haldarsaurav/train_bus_weather_signboard/docs/images/screen_boot.png

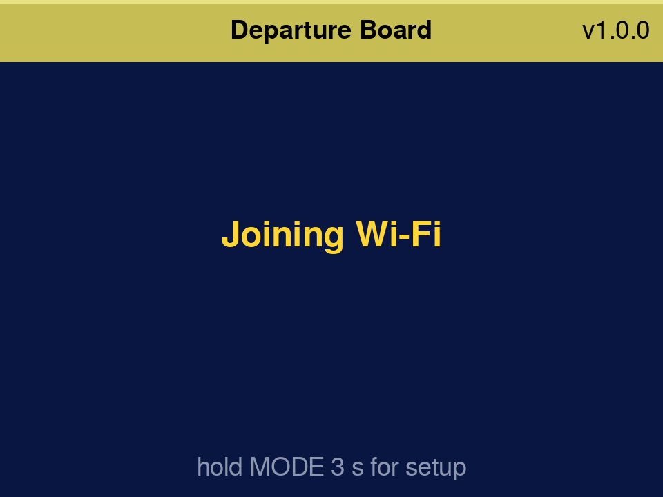
docs/images/screen_boot.png
