haldarsaurav/train_bus_weather_signboard/docs/images/screen_hold_hint.png

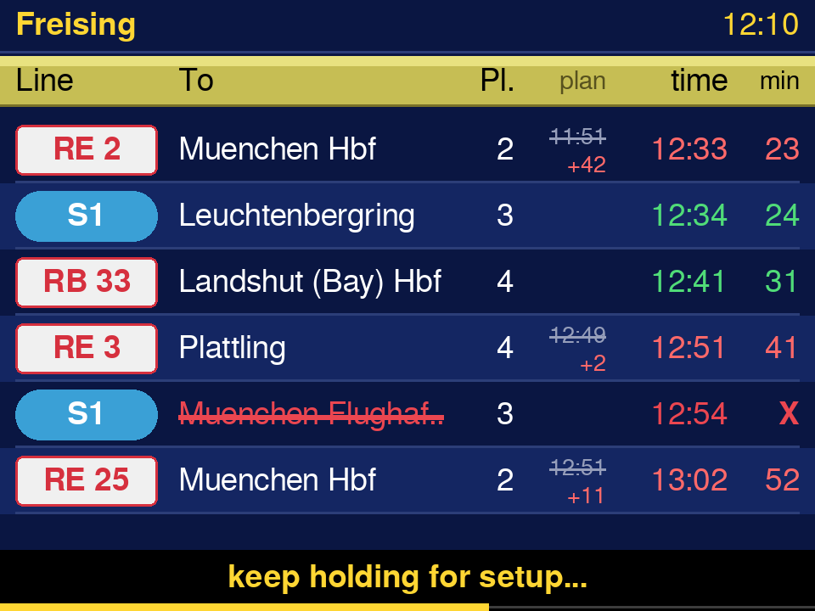
docs/images/screen_hold_hint.png
