haldarsaurav/train_bus_weather_signboard/docs/previews_v1.2.0/A_1_boot.png

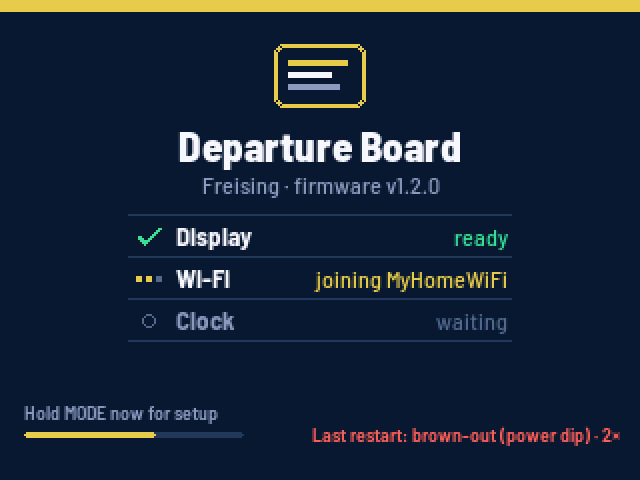
docs/previews_v1.2.0/A_1_boot.png
