haldarsaurav/train_bus_weather_signboard/docs/previews_v1.2.0/A_4_pr.png

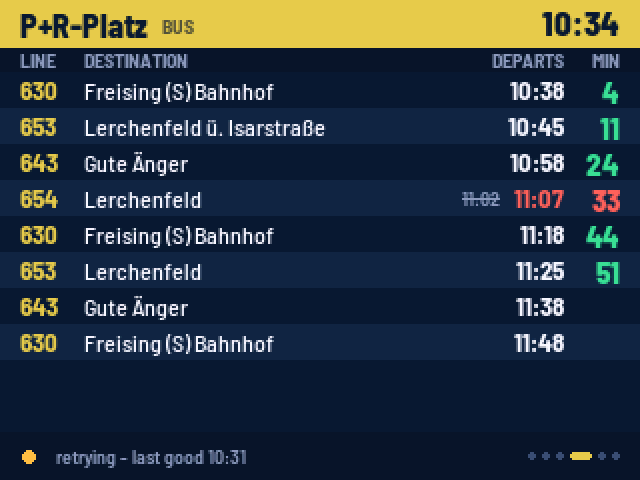
docs/previews_v1.2.0/A_4_pr.png
