haldarsaurav/train_bus_weather_signboard/docs/previews_v1.2.0/B_1_boot.png

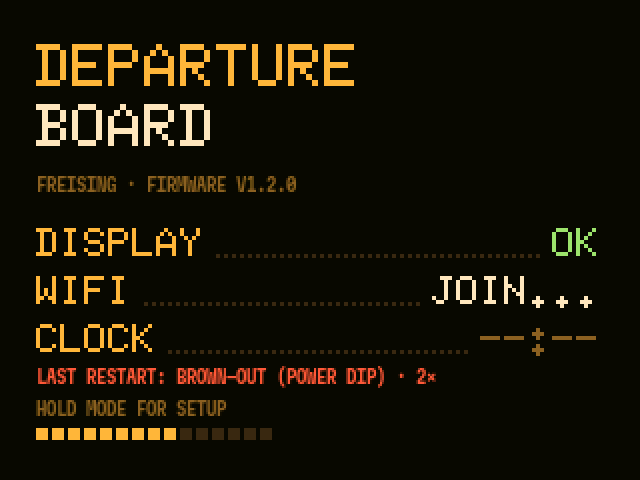
docs/previews_v1.2.0/B_1_boot.png
