haldarsaurav/train_bus_weather_signboard/docs/previews_v1.2.0/B_7_hold.png

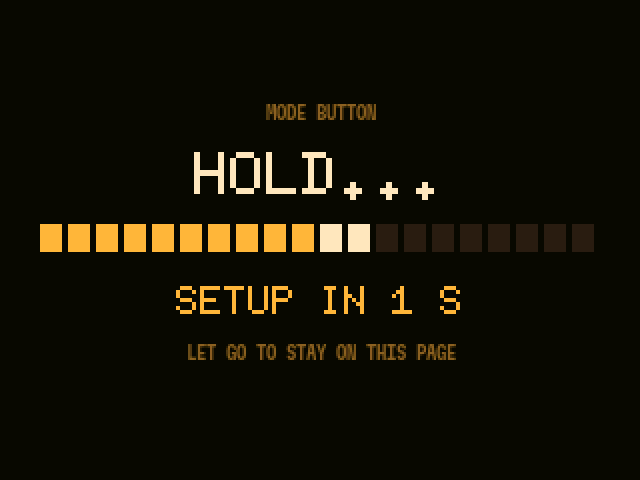
docs/previews_v1.2.0/B_7_hold.png
