haldarsaurav/train_bus_weather_signboard/docs/previews_v1.2.0/C_1_boot.png

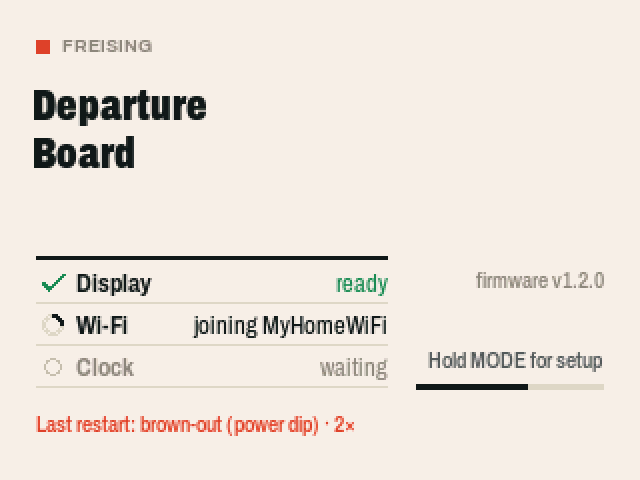
docs/previews_v1.2.0/C_1_boot.png
