haldarsaurav/train_bus_weather_signboard/docs/previews_v1.2.0/C_2b_trains_page2.png

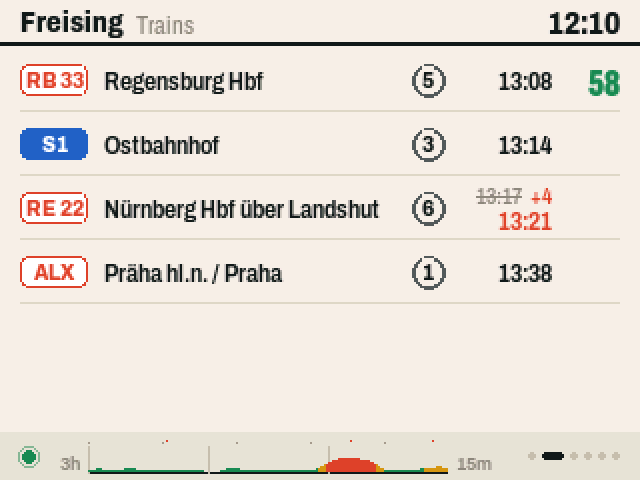
docs/previews_v1.2.0/C_2b_trains_page2.png
