haldarsaurav/train_bus_weather_signboard/docs/previews_v1.2.0/F_3_stadtbus.png

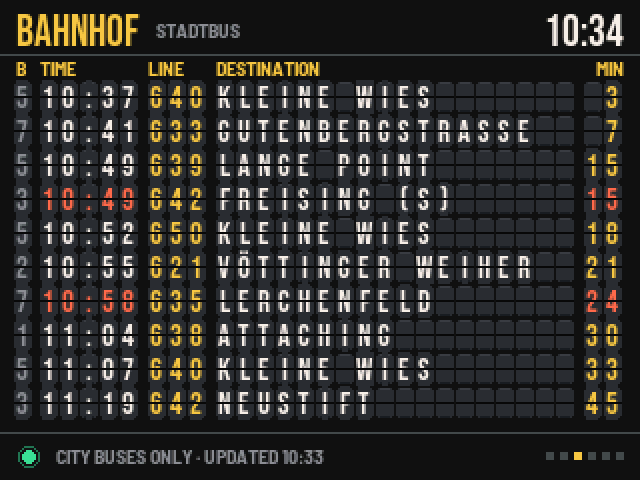
docs/previews_v1.2.0/F_3_stadtbus.png
