haldarsaurav/train_bus_weather_signboard/docs/previews_v1.2.0/F_4_pr.png

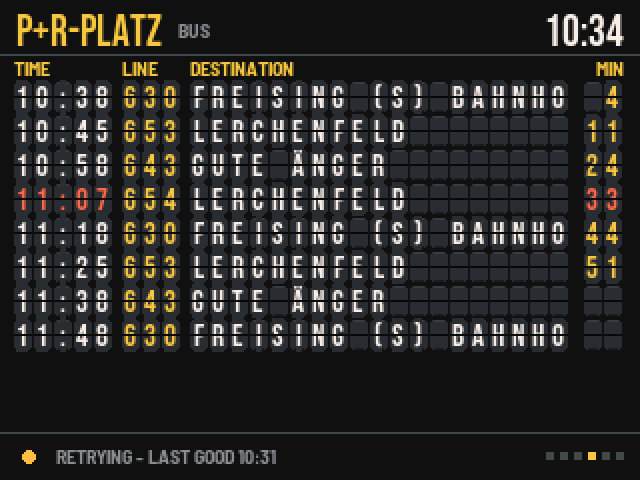
docs/previews_v1.2.0/F_4_pr.png
