haldarsaurav/train_bus_weather_signboard/docs/previews_v1.2.0/F_stress_umlauts_emoji.png

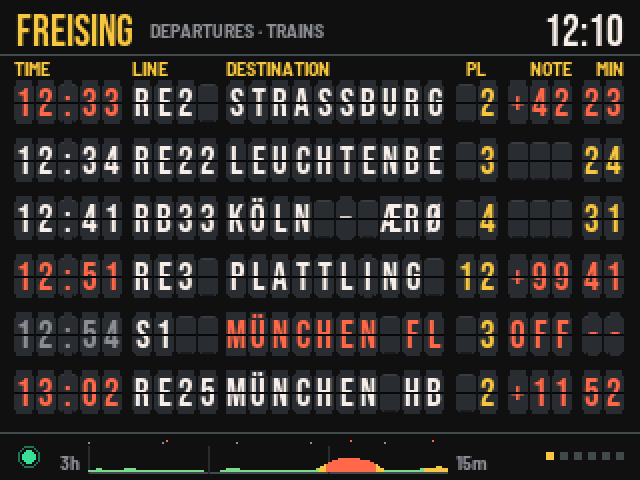
docs/previews_v1.2.0/F_stress_umlauts_emoji.png
