haldarsaurav/train_bus_weather_signboard/docs/previews_v1.2.0/O_5_weather.png

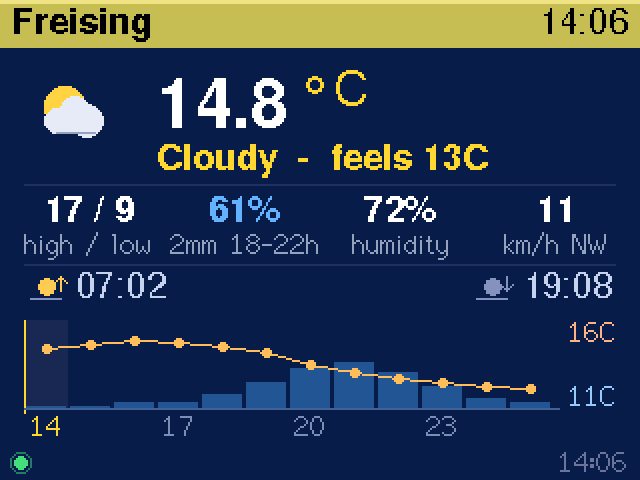
docs/previews_v1.2.0/O_5_weather.png
