haldarsaurav/train_bus_weather_signboard/docs/previews_v1.2.0/O_9_empty_trains.png

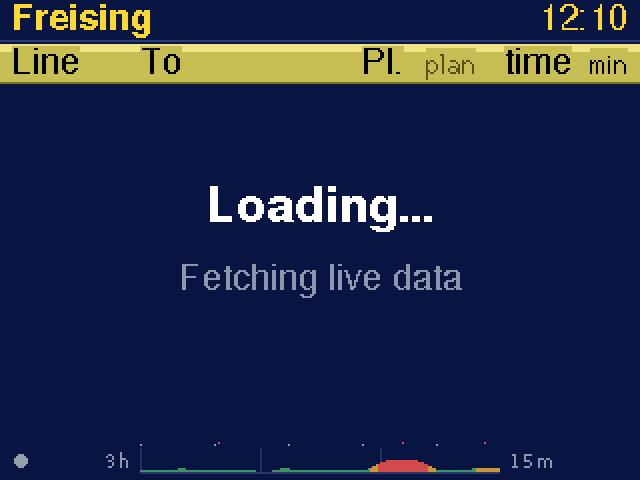
docs/previews_v1.2.0/O_9_empty_trains.png
