haldarsaurav/train_bus_weather_signboard/docs/previews_v1.2.0/portal_1.png

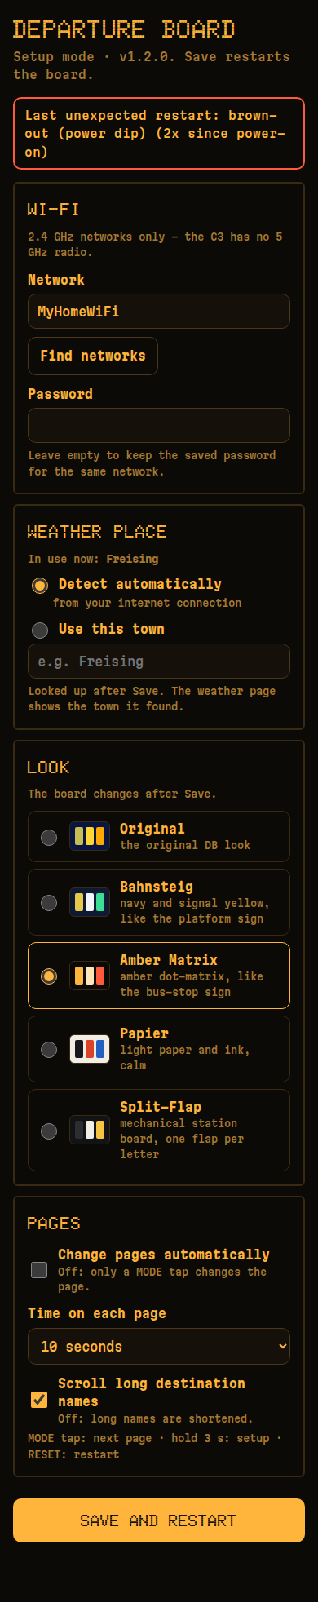
docs/previews_v1.2.0/portal_1.png
