haldarsaurav/train_bus_weather_signboard/docs/images/screen_setup.png

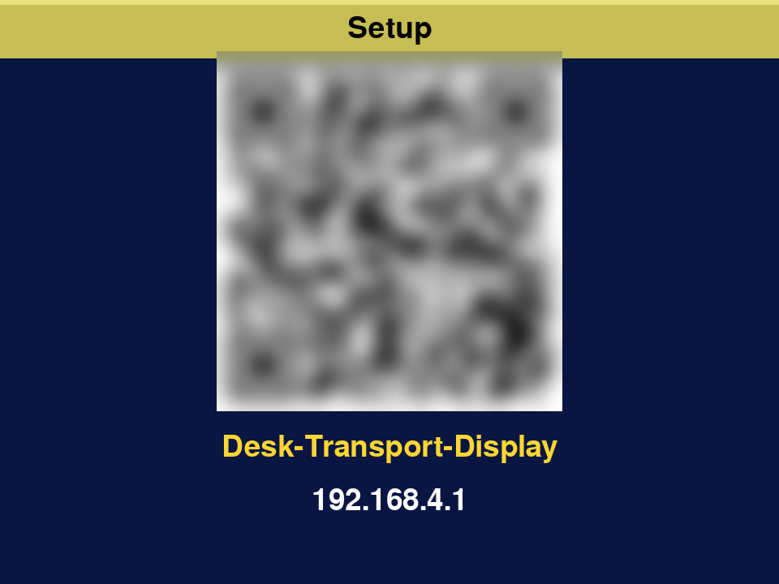
docs/images/screen_setup.png
