haldarsaurav/train_bus_weather_signboard/docs/images/wiring.png

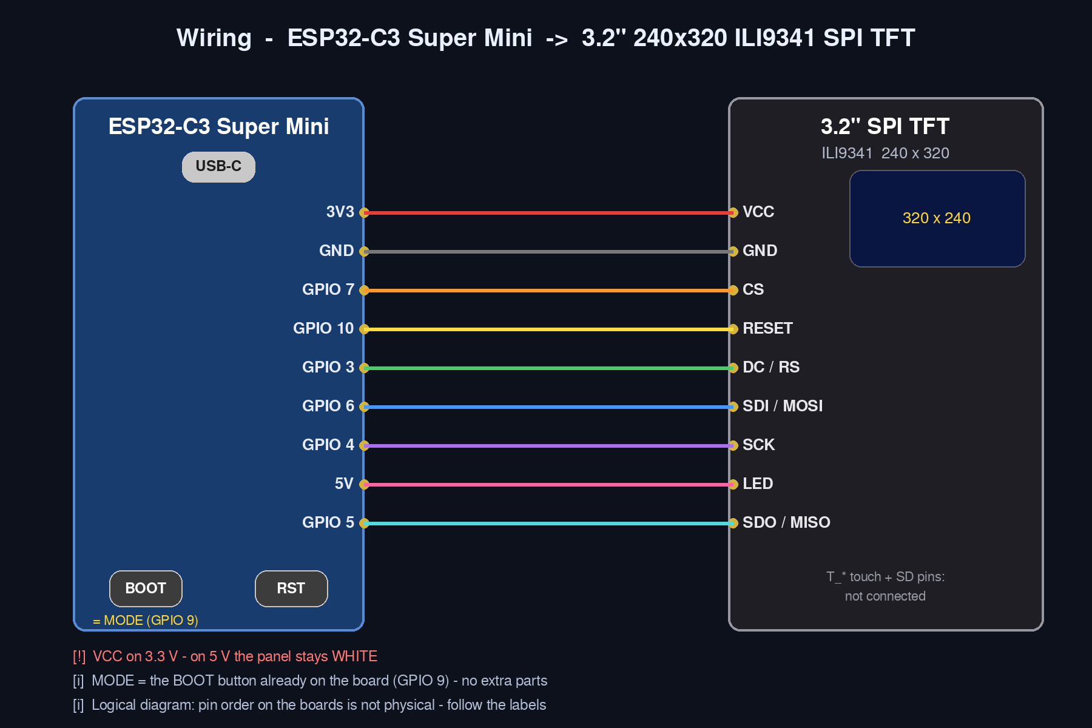
docs/images/wiring.png
