haldarsaurav/train_bus_weather_signboard/docs/previews_v1.2.0/A_8b_setup_phone.png

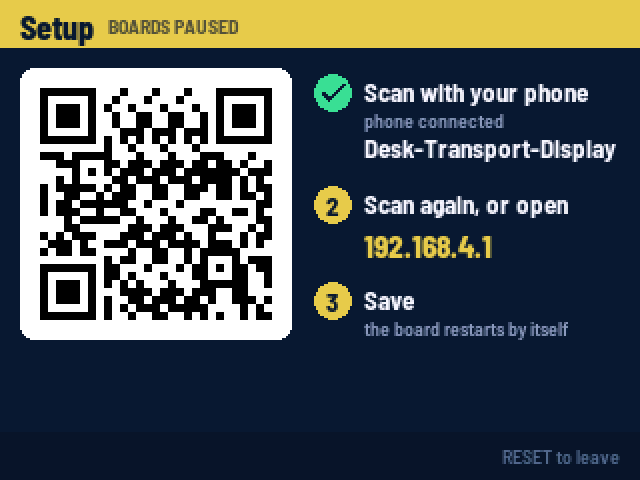
docs/previews_v1.2.0/A_8b_setup_phone.png
